PepaAp/DIY-steering-wheel/stl/volant/loziska/drzak na lozisko v bedne dodatek.stl

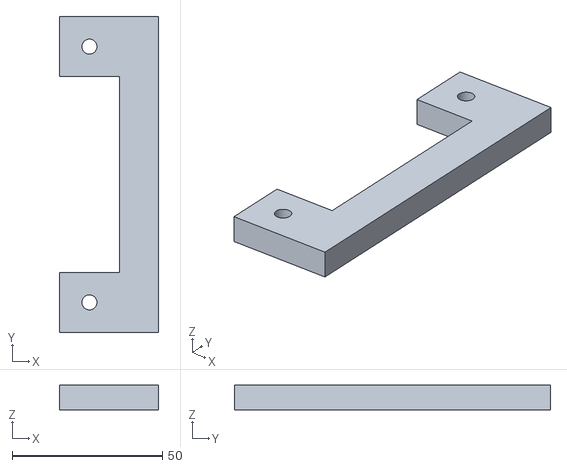
[picture p15: CAD file, 2026-05-04]
stl/volant/loziska/drzak na lozisko v bedne dodatek.stl
33.0 x 105.0 x 8.20
