PepaAp/DIY-steering-wheel/stl/volant/packy/prototypy/krytka hlavni v8.stl

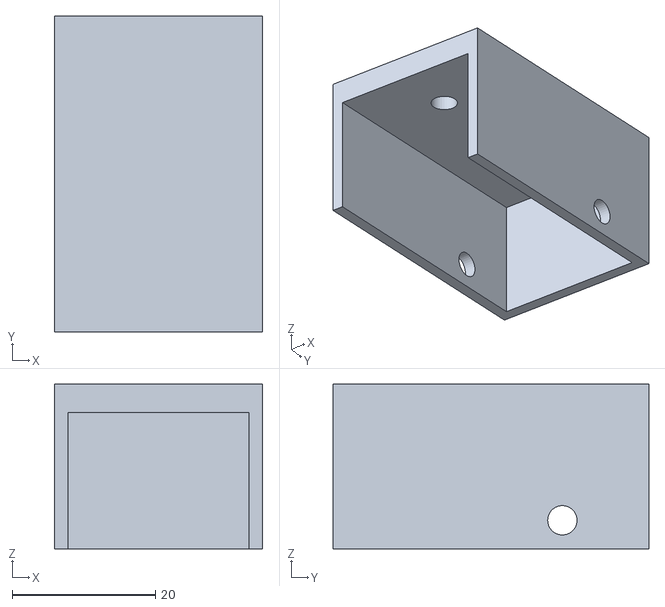
[picture p16: CAD file, 2026-05-04]
stl/volant/packy/prototypy/krytka hlavni v8.stl
29.0 x 44.0 x 23.0
