PepaAp/DIY-steering-wheel/stl/volant/loziska/gearwheel 30 bigger v1.stl

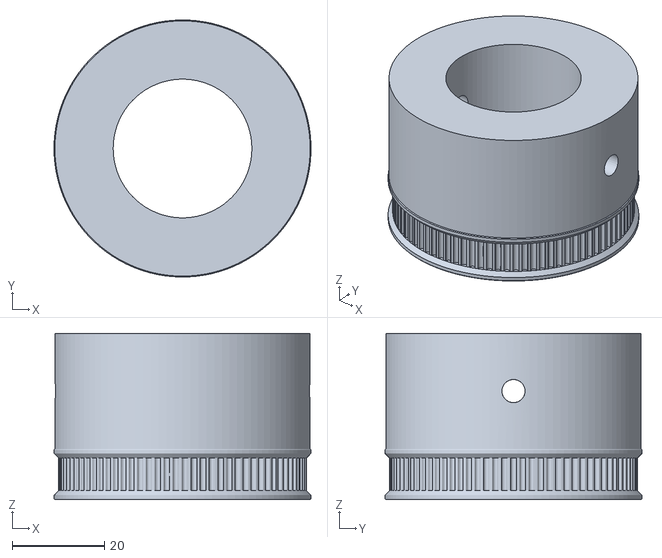
[picture p17: CAD file, 2026-05-04]
stl/volant/loziska/gearwheel 30 bigger v1.stl
55.6 x 55.6 x 36.0
