PepaAp/DIY-steering-wheel/stl/volant/packy/prototypy/packa mala ohyb.stl

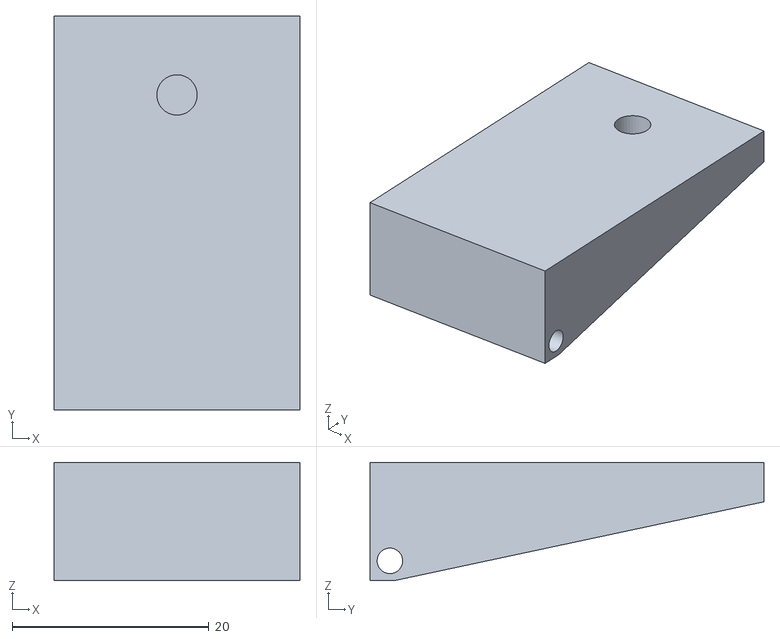
[picture p18: CAD file, 2026-05-04]
stl/volant/packy/prototypy/packa mala ohyb.stl
25.0 x 40.0 x 12.0
