PepaAp/DIY-steering-wheel/stl/volant/packy/prototypy/packa mala ohyb v8.3mf

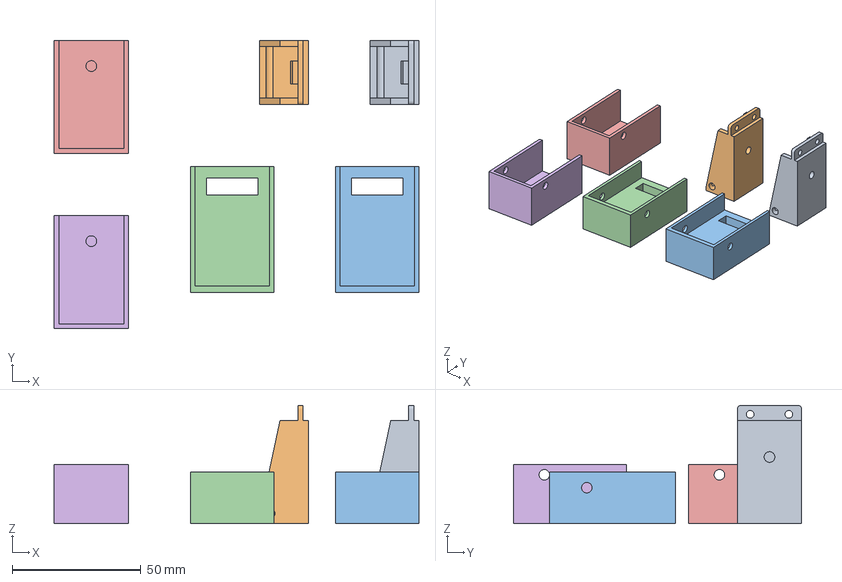
[picture p19: CAD file, 2026-05-04]
stl/volant/packy/prototypy/packa mala ohyb v8.3mf
141.7 x 112.0 x 46.0 mm
packa mala ohyb v8.stl x 2
horni dil v2.stl x 2
krytka hlavni v8.stl x 2
