PepaAp/DIY-steering-wheel/stl/volant/packy/prototypy/horni dil v2.stl

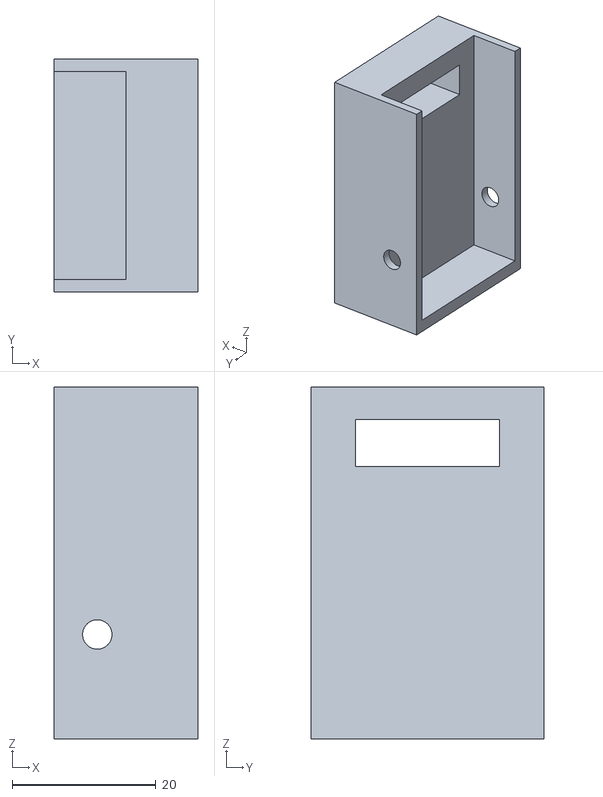
[picture p20: CAD file, 2026-05-04]
stl/volant/packy/prototypy/horni dil v2.stl
20.0 x 32.4 x 49.0
